platevoltage/RC-transmitter/src/Transmitter.cpp

#include "Transmitter.h"



uint8_t Transmitter::broadcastAddress[6];

Transmitter::Transmitter() {
    
}
Transmitter::~Transmitter() {}

void Transmitter::OnDataSent(const uint8_t *mac_addr, esp_now_send_status_t status) {
    // Serial.print("Last Packet Send Status: ");
    // if (status == ESP_NOW_SEND_SUCCESS) {
    //     Serial.println("Delivery Success");
    // } else {
    //     Serial.println("Delivery Fail");
    // }
}

void Transmitter::init(const uint8_t *receiverMacAddress) {

    memcpy(broadcastAddress, receiverMacAddress, 6);

    Serial.println("Initialize ESP-NOW");
    // Set device as a Wi-Fi Station
    WiFi.mode(WIFI_STA);
    esp_wifi_set_max_tx_power(84);
    esp_wifi_set_protocol(WIFI_IF_STA, WIFI_PROTOCOL_LR);

    // Initialize ESP-NOW
    if (esp_now_init() != ESP_OK) {
        Serial.println("Error initializing ESP-NOW");
        return;
    }

    // Register callback function
    esp_now_register_send_cb(OnDataSent);

    // Clear the peerInfo structure
    esp_now_peer_info_t peerInfo = {};
    memcpy(peerInfo.peer_addr, broadcastAddress, 6);
    peerInfo.channel = 0;
    peerInfo.encrypt = false;

    // Check if the peer already exists
    if (esp_now_is_peer_exist(broadcastAddress)) {
        Serial.println("Peer already exists. Deleting and adding again.");
        if (esp_now_del_peer(broadcastAddress) != ESP_OK) {
            Serial.println("Failed to delete existing peer");
            return;
        }
    }

    // Add peer
    esp_err_t addStatus = esp_now_add_peer(&peerInfo);
    if (addStatus != ESP_OK) {
        Serial.println("Failed to add peer");
        Serial.print("Error code: ");
        Serial.println(addStatus);
        Serial.print("Peer MAC Address: ");
        for (int i = 0; i < 6; i++) {
            Serial.printf("%02X", broadcastAddress[i]);
            if (i < 5) Serial.print(":");
        }
        Serial.println();
        return;
    }
    Serial.println("Peer added successfully");
}

esp_err_t Transmitter::sendData(struct_message message) {
    esp_err_t result = esp_now_send(broadcastAddress, (uint8_t *) &message, sizeof(message));
    // Serial.print("ACCELERATOR - ");
    // Serial.print(message.accelerator);
    // Serial.print("   BRAKE - ");
    // Serial.print(message.brake);
    // Serial.print("   DRIVE - ");
    // Serial.print(message.drive);
    // Serial.print("   STEER - ");
    // Serial.print(message.steering);
    // if (result == ESP_OK) {
    //     Serial.println("   Sent with success");
    // } else {
    //     Serial.println("   Error sending the data");
    // }
    return result;
}
